jpgoyret/tp-final-ruiz-goyret-DCE-FIUBA-1C2019/Supply/mediciones_supply/Mediciones_supply_5_7_19.md

## Mediciones fuente switching

Fuente: MCP M10-SP3010L

Osciloscopio: Tektronix TDS1001B

Multímetro: UNI-Y UT33A

###### Mediciones de eficiencia

V_in = 17,36 V

I_in = 47,3 mA

V_out = 12,04 V

I_out = 48 mA

Entonces:

P_in = 814 mW

P_out = 576 mW

Eficiencia = (P_in/P_out)*100% = 70 %
