jpgoyret/tp-final-ruiz-goyret-DCE-FIUBA-1C2019/DOC/README.md

## Carpeta DOC (documentos varios)

- En el archivo [Referencias.md](Referencias.md) se puede encontrar un listado de documentos y libros que sirvieron como base para el desarrollo del proyecto.
- En [comparacion_amplificadores_comerciales](comparacion_amplificadores_comerciales.xlsx) se encuentra una comparación entre algunos amplificadores investigados durante la etapa de diseño.
- En [datasheets_amplificadores_comerciales](./datasheets_amplificadores_comerciales) se pueden encontrar hojas de datos de algunos amplificadores investigados.
