jpgoyret/tp-final-ruiz-goyret-DCE-FIUBA-1C2019/Amplificador/mediciones_amplificador/README.md

## Registro de las mediciones realizadas durante el armado del amplificador

En el archivo [mediciones_finales.md](mediciones_finales.md) se encuentras las mediciones finales realizadas sobre el amplificador, las cuales han sido tomadas como punto de comparación con las especificaciones teóricas y las simuladas.

Además, en esta carpeta se incluye un registro de las mediciones realizadas durante el armado del amplificador, identificadas por fecha según el progreso que se fue realizando. Las fechas de las mediciones fueron las siguientes:

- [5/7/19](Mediciones_amplificador_5_7_19.md)
- [10/7/19](Mediciones_amplificador_10_7_19.md)
- [12/7/19](Mediciones_amplificador_12_7_19.md)
- [19/7/19](Mediciones_amplificador_19_7_19.md)

En los siguientes archivos podrá encontrarse la caracterización de las protecciones del amplificador:

- [Limitadores de sobrecorriente](caracterizacion_limitadores_sobrecorriente.md)
- [Protección de la carga contra DC en la salida](caracterizacion_proteccion_DC.md)
