jpgoyret/tp-final-ruiz-goyret-DCE-FIUBA-1C2019/Amplificador/simulaciones_amplificador/README.md

### Simulaciones del amplificador

Aquí se encuentra la información referida a las simulaciones realizadas del amplificador. En el archivo [Mediciones_parametros_simulacion.md](Mediciones_parametros_simulacion.md) se pueden encontrar los resultados de las simulaciones. Por otra parte, se proveen los archivos de simulación que permitieron medir toda la información recabada en ese último archivo.
