jpgoyret/tp-final-ruiz-goyret-DCE-FIUBA-1C2019/Amplificador/imagenes_amplificador/esquema_filtro.png

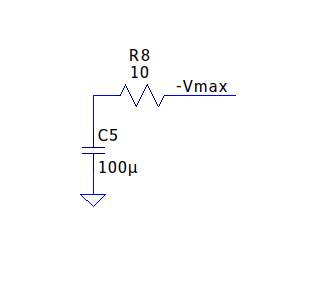
Amplificador/imagenes_amplificador/esquema_filtro.png
