jpgoyret/tp-final-ruiz-goyret-DCE-FIUBA-1C2019/Amplificador/imagenes_amplificador/medicion_velocidad_respuesta_proteccion_DC.png

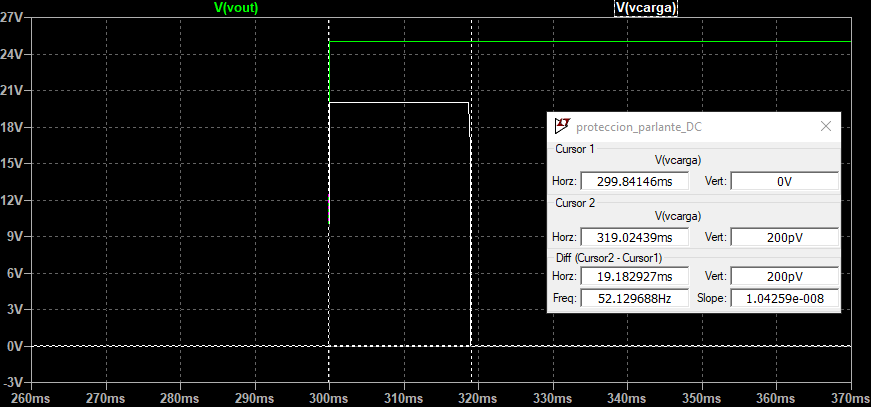
Amplificador/imagenes_amplificador/medicion_velocidad_respuesta_proteccion_DC.png
