jpgoyret/tp-final-ruiz-goyret-DCE-FIUBA-1C2019/Amplificador/imagenes_amplificador/mediciones_amplificador/fotos_caracterizacion_proteccion_DC/circuito_medicion_proteccion_DC.jpeg

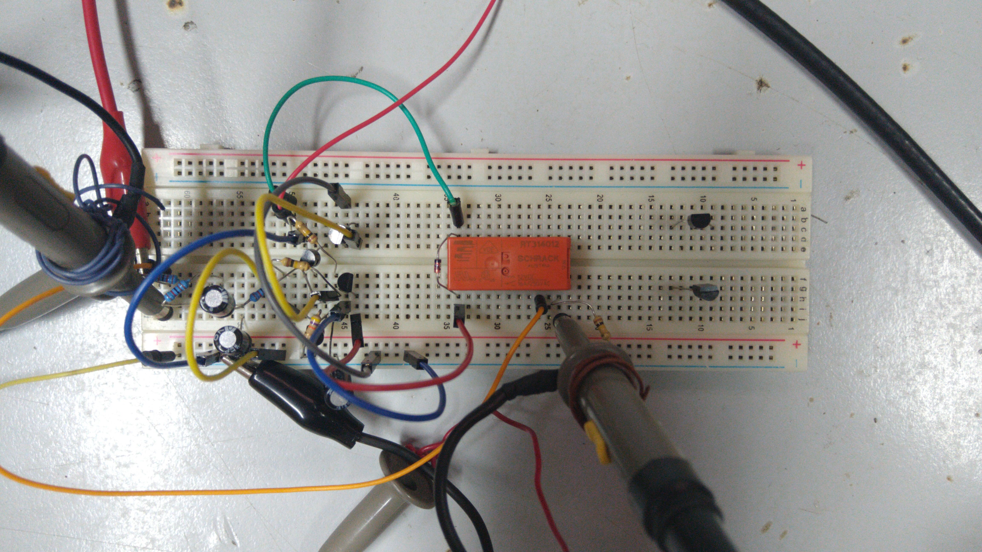
Amplificador/imagenes_amplificador/mediciones_amplificador/fotos_caracterizacion_proteccion_DC/circuito_medicion_proteccion_DC.jpeg
