jpgoyret/tp-final-ruiz-goyret-DCE-FIUBA-1C2019/Amplificador/imagenes_amplificador/mediciones_amplificador/fotos_caracterizacion_proteccion_DC/esquematico_medicion_proteccion_DC.png

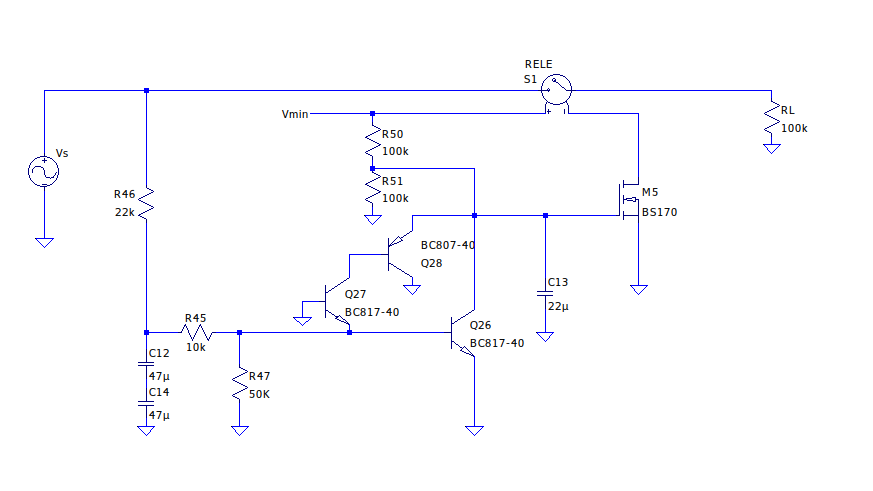
Amplificador/imagenes_amplificador/mediciones_amplificador/fotos_caracterizacion_proteccion_DC/esquematico_medicion_proteccion_DC.png
