jpgoyret/tp-final-ruiz-goyret-DCE-FIUBA-1C2019/Amplificador/imagenes_amplificador/mediciones_amplificador/fotos_caracterizacion_proteccion_DC/rele_15V_tiempo_respuesta.jpg

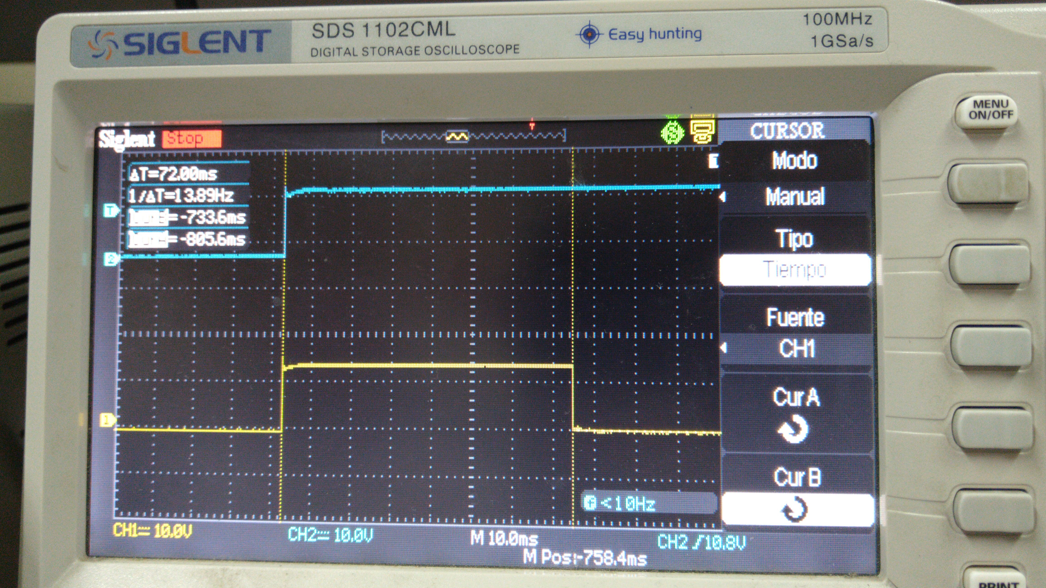
Amplificador/imagenes_amplificador/mediciones_amplificador/fotos_caracterizacion_proteccion_DC/rele_15V_tiempo_respuesta.jpg
