jpgoyret/tp-final-ruiz-goyret-DCE-FIUBA-1C2019/Supply/imagenes_supply/foto_prototipo_dimensiones.jpg

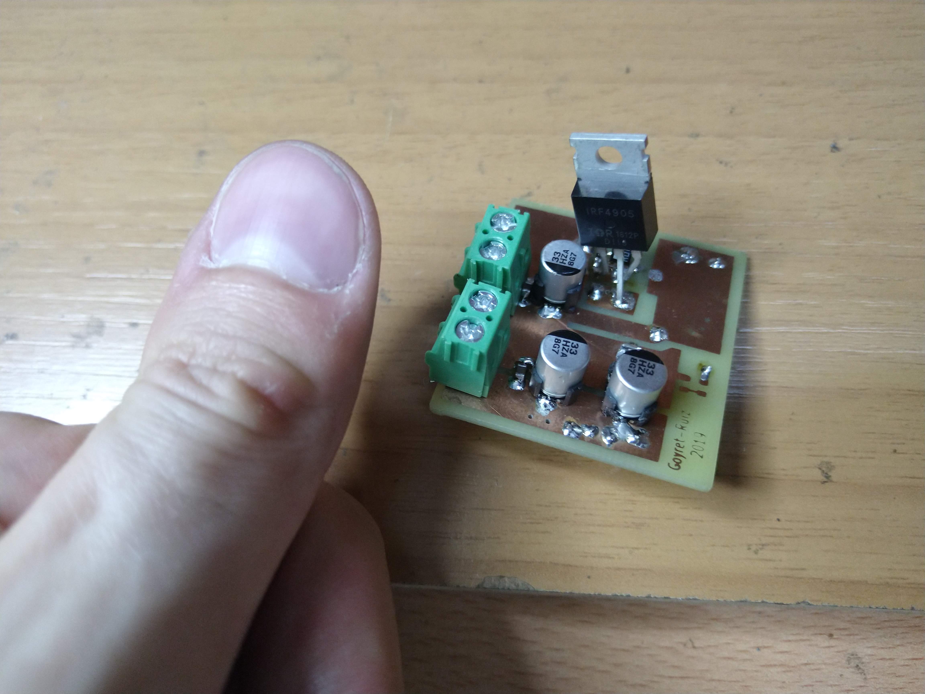
Supply/imagenes_supply/foto_prototipo_dimensiones.jpg
