jpgoyret/tp-final-ruiz-goyret-DCE-FIUBA-1C2019/Supply/mediciones_supply/fotos_mediciones_15_7_19/IMG_20190715_203706.jpg

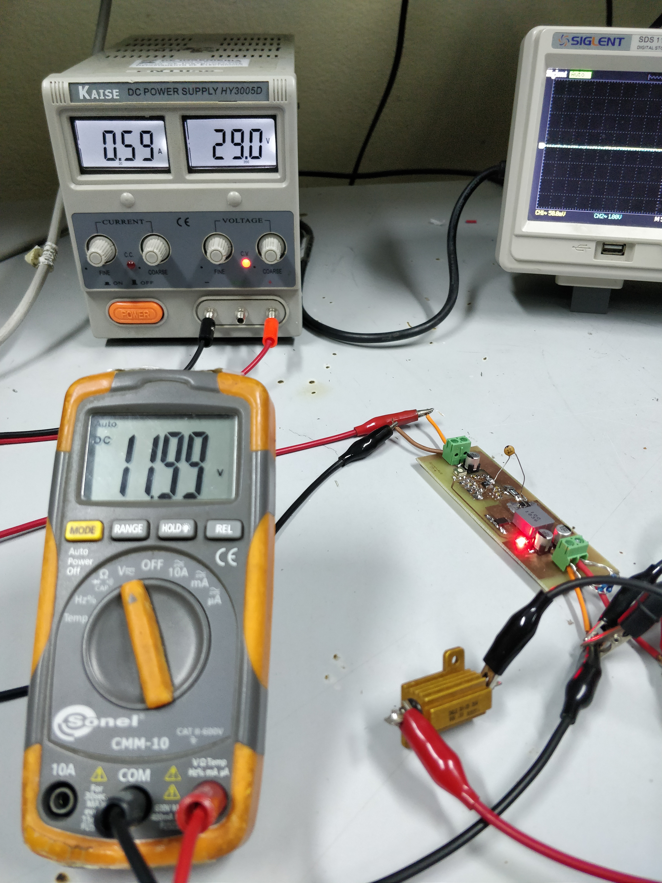
Supply/mediciones_supply/fotos_mediciones_15_7_19/IMG_20190715_203706.jpg
