jpgoyret/tp-final-ruiz-goyret-DCE-FIUBA-1C2019/Amplificador/simulaciones_amplificador/amplificador_completo_prueba_accion_proteccion_DC.asc

C1: cap; 47µ
C2: cap; 470µ
C3: cap; 1000µ
C4: cap; 33p
C5: cap; 10µ
C6: cap; 33n
C7: cap; 47µ
C8: cap; 1000µ
C9: cap; 10µ
C10: cap; 1000µ
C11: cap; 1µ
C12: cap; 47µ
C13: cap; 22µ
C14: cap; 47µ
D3: diode; 1N4148
D4: diode; 1N4148
D5: diode; 1N4148
D6: diode; 1N4148
D7: diode; 1N4148
D8: diode; 1N4148
D9: diode; 1N4148
D10: diode; 1N4148
D11: diode; 1N4148
D12: diode; 1N4148
D13: diode; 1N4148
D14: diode; 1N4148
D15: schottky; MBR735
D16: schottky; MBR735
D17: diode; 1N4148
D18: diode; 1N4148
D19: diode; 1N4148
D20: diode; 1N4148
D21: diode; 1N4148
D22: diode; 1N4148
M1: pmos; FDS9934_P
M2: pmos; FDS9934_P
M3: nmos; FDS9934_N
M4: nmos; FDS9934_N
M5: nmos; BS170
Q1: pnp; BC857C
Q2: pnp; BC857C
Q3: npn; BC847C
Q4: npn; BC847C
Q5: pnp; BC857C
Q6: pnp; BC857C
Q7: npn; BC847C
Q8: npn; 2SCR514P
Q9: npn; 2SCR514P
Q10: npn; BD139
Q11: pnp; BD140
Q12: npn; BD139
Q13: pnp; MJL1302A
Q14: npn; MJL3281A
Q15: pnp; MJL1302A
Q16: npn; MJL3281A
Q17: pnp; 2SAR514P
Q18: pnp; BC857C
Q19: pnp; BC857C
Q20: pnp; 2SAR514P
Q21: npn; 2SCR514P
Q22: pnp; 2SAR514P
Q23: npn; 2SCR514P
Q24: pnp; 2SAR514P
Q25: npn; 2SCR514P
Q26: npn; BC817-40
Q27: npn; BC817-40
Q28: pnp; BC807-40
R1: res; 120
R2: res; 120
R3: res; 68
R4: res; 68
R5: res; 15k
R6: res; 10
R7: res; 2.2k
R8: res; 10
R9: res; 2k
R10: res; 770
R11: res; 50
R12: res; 50
R13: res; 16
R14: res; 1k
R15: res; 270
R16: res; 330
R17: res; 68
R18: res; 3.9k
R19: res; 680
R20: res; 10k
R21: res; 10k
R22: res; 2.2k
R23: res; 110
R24: res; 50
R25: res; 1.1k
R26: res; 1.1k
R27: res; 0.1
R28: res; 0.1
R29: res; 1k
R30: res; 1k
R31: res; 1k
R32: res; 3k
R33: res; 1k
R34: res; 1k
R35: res; 1k
R36: res; 3k
R37: res; 11k
R38: res; 330
R39: res; 270
R40: res; 11k
R41: res; 3.3
R42: res; 3.3
R43: res; 2.2k
R44: res; 5
R45: res; 10k
R46: res; 22k
R47: res; 50K
R48: res; 4
R49: res; 600
R50: res; 100k
R51: res; 100k
S1: sw; MYSW
S2: sw; Sbreak
V1: voltage; 12
V2: voltage; 30
V3: voltage; -12
V4: voltage; -30
V5: signal; SINE(0 0 10K); AC 1m
V6: voltage; PULSE(0 10 0.5m 1000n 1000n 1 4)
V7: voltage; 30
Named nets: 0, Vmin, Vmax, -Vmin, -Vmax, vin, Vout, SW1
.include modelos/MJL.lib
Baja potencia
Alta potencia
Baja potencia
Alta potencia
;ac dec 10m 0.1 100meg
.tran 0 500m 0
.include modelos/BD139.LIB
.include modelos/BD140.LIB
.model MYSW SW(Vt=11 Ron=0.0001 Roff=1Meg)
.model Sbreak SW(Ron=1 Roff=1Meg Vt=5 Vh=0 Lser=0 Vser=0)
.include modelos/BS170.LIB
