jpgoyret/tp-final-ruiz-goyret-DCE-FIUBA-1C2019/Amplificador/simulaciones_amplificador/test_proteccion_sobrecorriente.asc

IR: current; 4
Q1: npn; 2SCR514P
R1: res; 11k
R2: res; 270
R3: res; 330
R4: res; 0.1
R5: res; 750
V1: voltage; 2
V2: voltage; 10
Named nets: 0
;tran 10m
.dc IR 0 20 1
Para una explicación del método de puesta
prueba de la protección por sobrecorriente ver
página 410 de "Audio Power Amplifier Handbook" de Douglas Self}
El valor de V1 representa la diferencia entre la alimentación conectada a R1
(en la práctica Vmax=30V) y la tensión de salida. 
Cuanto mayor es V1, mayor sería la tensión en el nodo de salida.
