jpgoyret/tp-final-ruiz-goyret-DCE-FIUBA-1C2019/Amplificador/simulaciones_amplificador/test_llaves_ambos_semiciclos.asc

D1: diode; 1N4148
D4: diode; 1N4148
D5: diode; 1N4148
D6: diode; 1N4148
D7: diode; 1N4148
D8: diode; 1N4148
D9: diode; 1N4148
D10: diode; 1N4148
D11: diode; 1N4148
D12: diode; 1N4148
D13: diode; 1N4148
D14: diode; 1N4148
D15: schottky; MBR735
D16: schottky; MBR735
M1: pmos; FDS9934_P
M2: pmos; FDS9934_P
M3: nmos; FDS9934_N
M4: nmos; FDS9934_N
Q20: pnp; 2SAR514P
Q21: npn; 2SCR514P
R1: res; 5k
R27: res; 0.1
R28: res; 0.1
R30: res; 1k
R31: res; 1k
R32: res; 2.7k
R33: res; 5k
R34: res; 1k
R35: res; 1.5k
R36: res; 2.7k
RL: res; 8
U1: 2SC5200
U2: 2SC5200
U3: 2SA1943
U4: 2SA1943
V1: voltage; 12
V2: voltage; 30
V3: voltage; -12
V4: voltage; -30
Vin: voltage; 15
Named nets: 0, Vmin, Vmax, -Vmin, -Vmax, Vout
.include modelos/MJL.lib
Baja potencia
Alta potencia
Baja potencia
Alta potencia
.dc Vin 1 30 1
Llave para el simiciclo inferior
Llave para el simiciclo superior
