jpgoyret/tp-final-ruiz-goyret-DCE-FIUBA-1C2019/Supply/simulaciones_supply/LTC3864.asc

C1: cap; 3300p
C2: cap; 470n
C3: cap; 10n
C4: cap; 100n
C5: cap; 3300p
C6: cap; 47µ
C7: cap; 22µ
C8: cap; 22µ; V=25 Rser=0.05
C9: cap; 47µ; Rser=1
Cob1: cap; 47µ; V=25 Rser=1
D1: schottky; PDS760
Lo1: ind; 10µ; Ipk=10 Rser=14m
M1: pmos; FDS4685
R1: res; 15m
R2: res; 8
R3: res; 10k
R4: res; 390k
R5: res; 33K
RfbBot1: res; 7.1k
RfbTop1: res; 100K
U1: LTC3864
V1: voltage; 28
Named nets: 0, IN
.tran 10m startup
;.meas Pin AVG -V(IN)*I(V1)
;.meas Pout AVG V(OUT)*I(I1)
;.meas Eff param Pout/Pin
;.step param Iload .2 3 1
