jpgoyret/tp-final-ruiz-goyret-DCE-FIUBA-1C2019/Amplificador/simulaciones_amplificador/multiplicador_vbe_elegir_capacitor.asc

C1: cap; {C}
I1: current; 10m
I2: current; SINE(0 0); AC 1m
I3: current; PULSE(0 10m 0 10m 10m 10m 40m)
Q1: npn; 2SCR514P
Q2: npn; 2SCR514P
R1: res; 2.2k
R2: res; 870
R3: res; 22
R4: res; 2.2k
R5: res; 870
R6: res; 22
Named nets: 0
.ac dec 10m 0.1 10g
;.step param R list 15 22 27
;tran 10m
Para determinar el valor óptimo de R13:
Para hallar el valor óptimo de C6:
.step param C list 33n 39n 47n
