jpgoyret/tp-final-ruiz-goyret-DCE-FIUBA-1C2019/Amplificador/simulaciones_amplificador/proteccion_parlante_DC.asc

C1: cap; 47µ
C2: cap; 22µ
C3: cap; 47µ
M1: nmos; BS170
Q1: npn; BC817-40
Q2: npn; BC817-40
Q3: pnp; BC807-40
R1: res; 22k
R2: res; 10k
R5: res; 50K
R8: res; 12k
R9: res; 100k
R10: res; 100k
RL: res; 4
S1: sw; MYSW
V2: voltage; 12
V3: voltage; PULSE(0 25 300m 1p 1p 1000m 5000m)
Named nets: 0
.tran 700m startup
.model MYSW SW(Vt=11)
.include modelos/bs170.lib
