jpgoyret/tp-final-ruiz-goyret-DCE-FIUBA-1C2019/Supply/mediciones_supply/fotos_mediciones_5_7_19/IMG_20190705_214144822.jpg

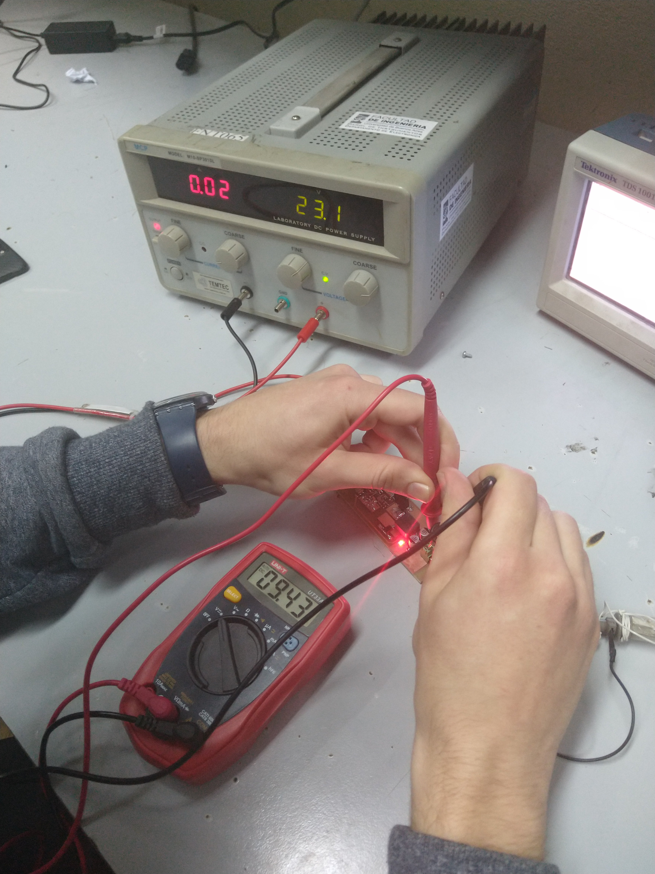
Supply/mediciones_supply/fotos_mediciones_5_7_19/IMG_20190705_214144822.jpg
